Filips-Talums/Battery_Power_Monitor/docs/images/B1AA8C16-F89B-4345-A86B-DF6DE2874C3C.JPG

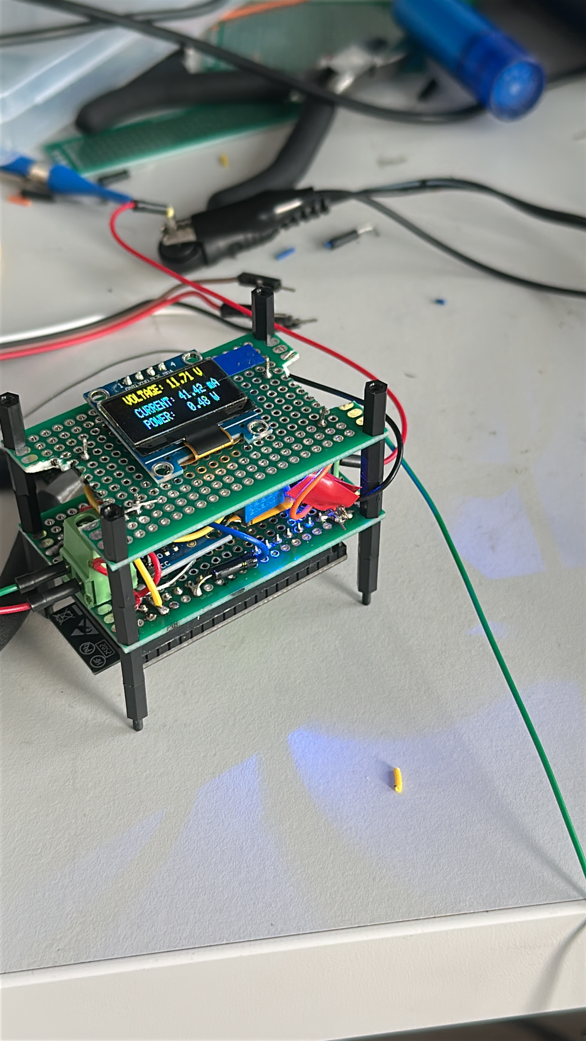
docs/images/B1AA8C16-F89B-4345-A86B-DF6DE2874C3C.JPG
