Filips-Talums/Battery_Power_Monitor/docs/images/IMG_2541.jpeg

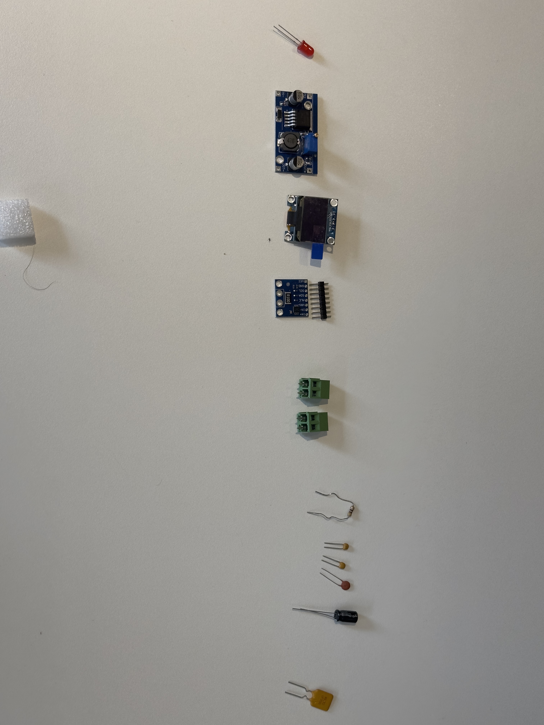
docs/images/IMG_2541.jpeg
