Filips-Talums/Battery_Power_Monitor/docs/images/IMG_2542.jpeg

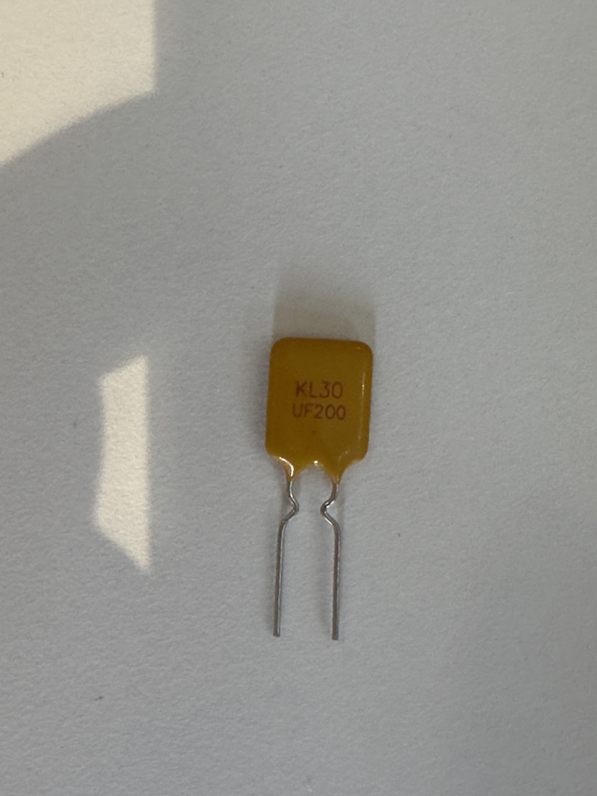
docs/images/IMG_2542.jpeg
