Filips-Talums/Battery_Power_Monitor/docs/images/IMG_2543.jpeg

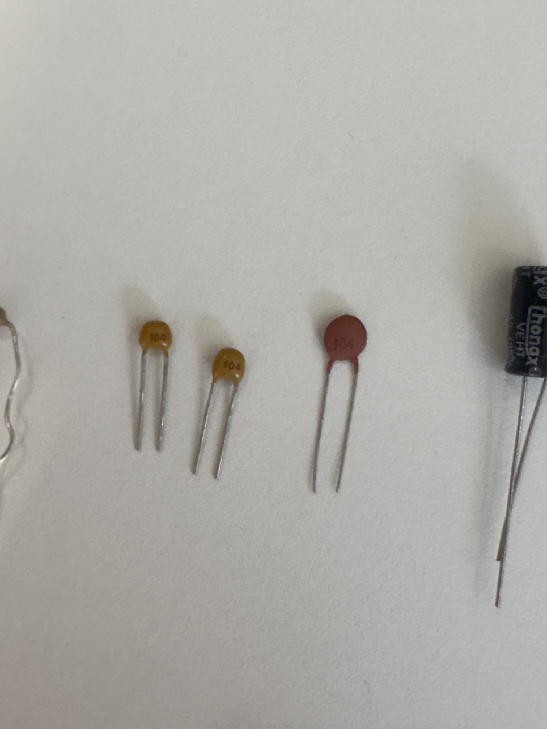
docs/images/IMG_2543.jpeg
