Filips-Talums/Battery_Power_Monitor/docs/images/IMG_2544.jpeg

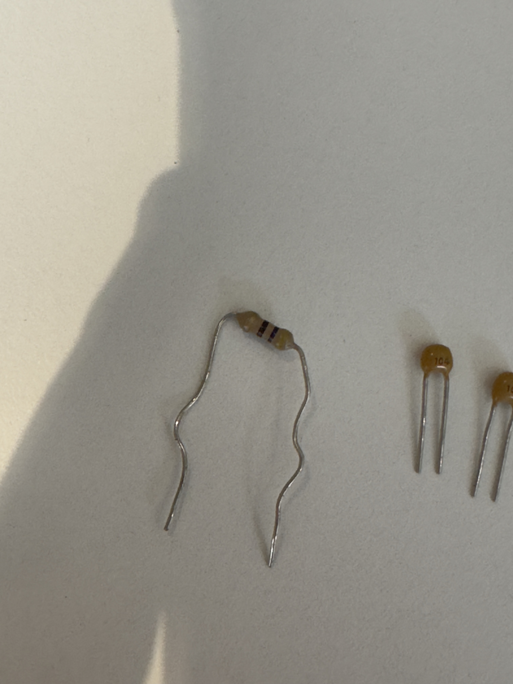
docs/images/IMG_2544.jpeg
