Filips-Talums/Battery_Power_Monitor/docs/images/IMG_2545.jpeg

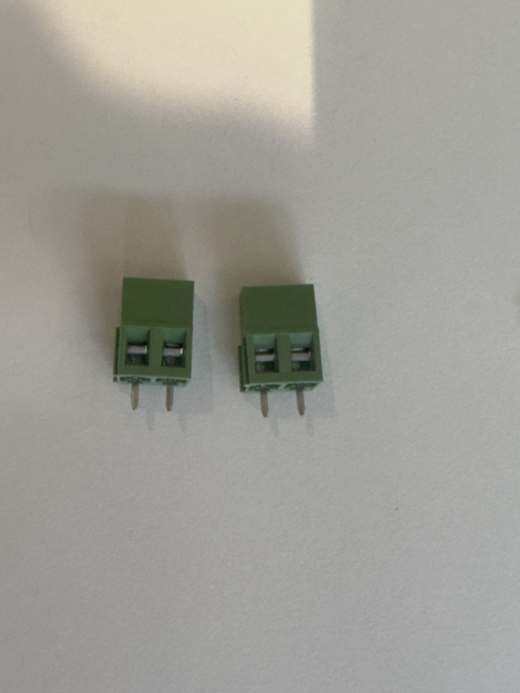
docs/images/IMG_2545.jpeg
