Filips-Talums/Battery_Power_Monitor/docs/images/IMG_2547.jpeg

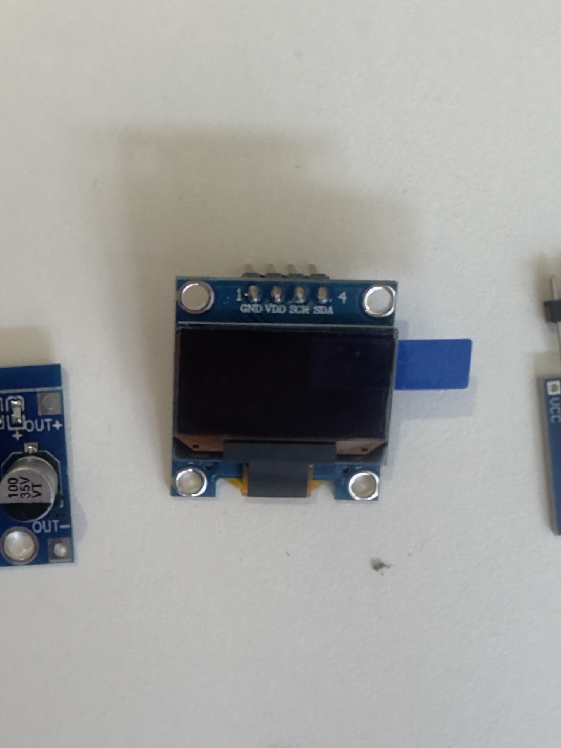
docs/images/IMG_2547.jpeg
