Filips-Talums/Battery_Power_Monitor/docs/images/IMG_2548.jpeg

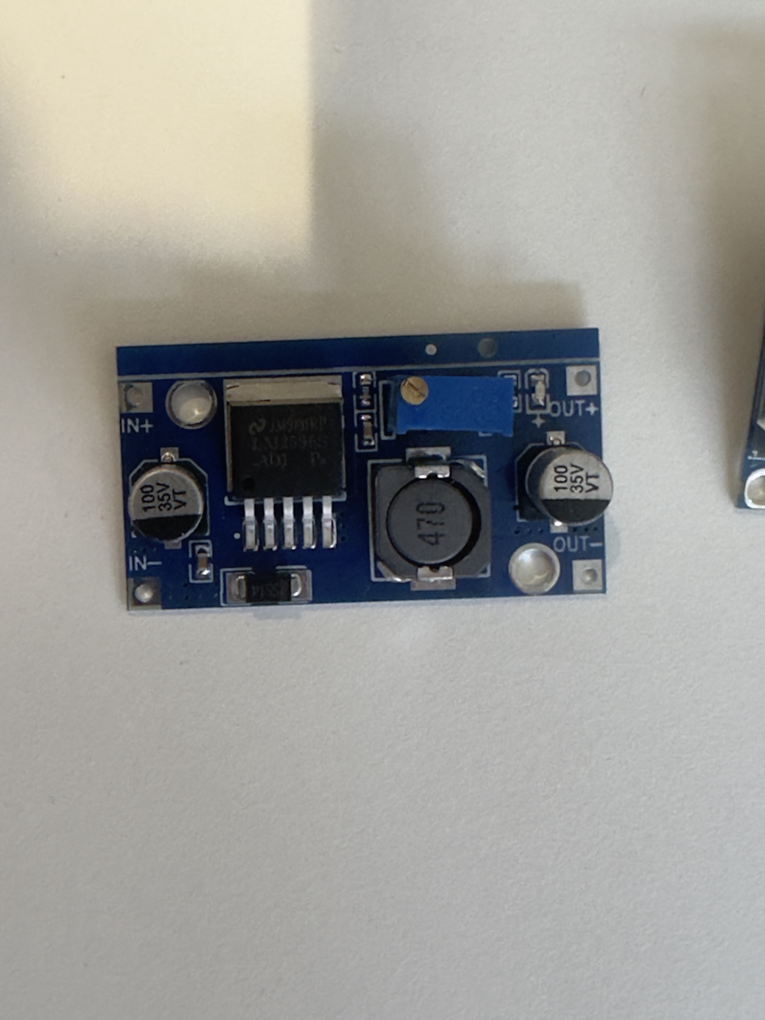
docs/images/IMG_2548.jpeg
