Filips-Talums/Battery_Power_Monitor/docs/images/IMG_2549.jpeg

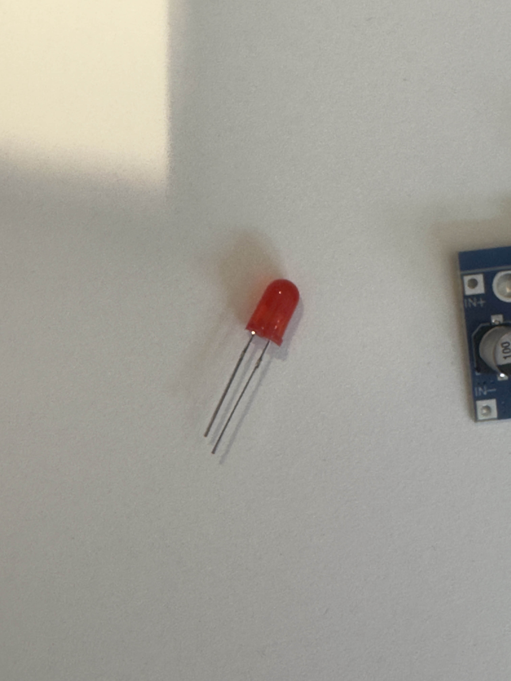
docs/images/IMG_2549.jpeg
