Filips-Talums/Battery_Power_Monitor/docs/images/IMG_2552.jpeg

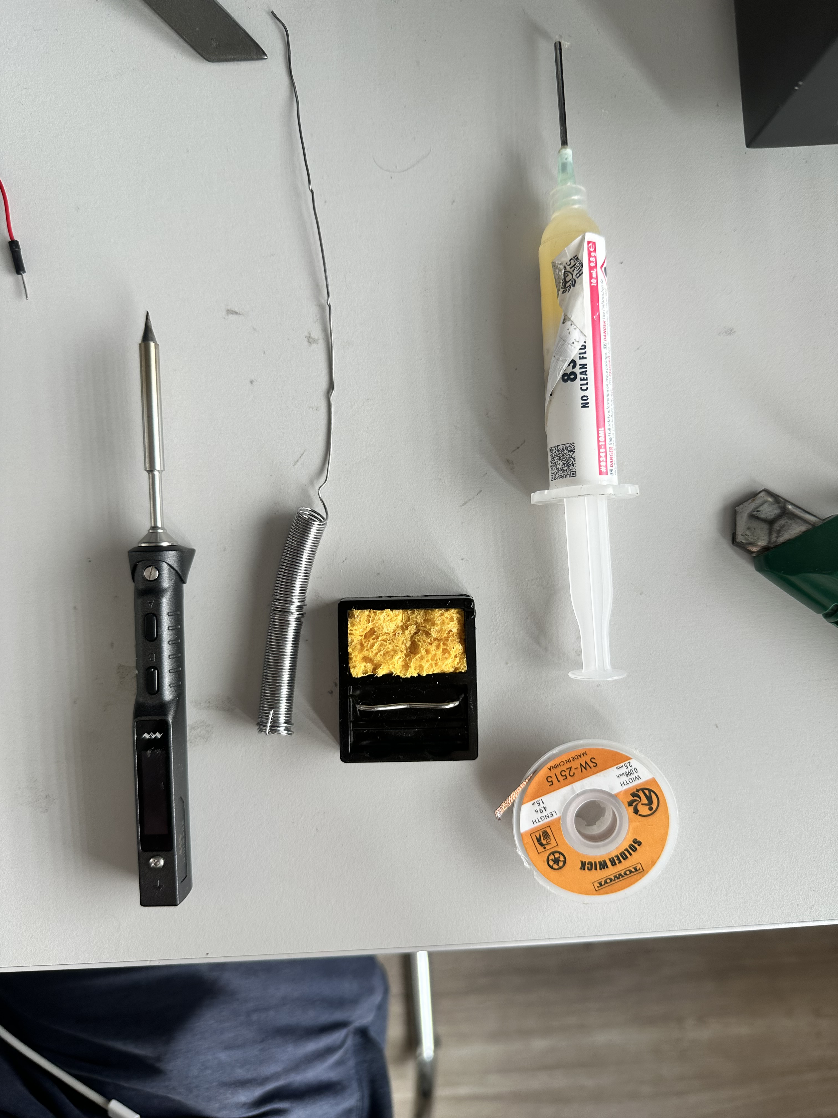
docs/images/IMG_2552.jpeg
