Filips-Talums/Battery_Power_Monitor/docs/images/IMG_2553.jpeg

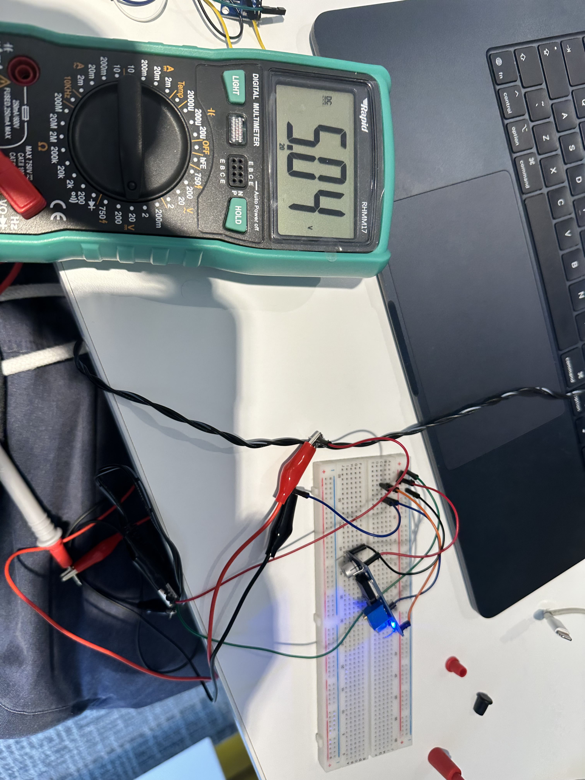
docs/images/IMG_2553.jpeg
