Filips-Talums/Battery_Power_Monitor/docs/images/IMG_2556.jpeg

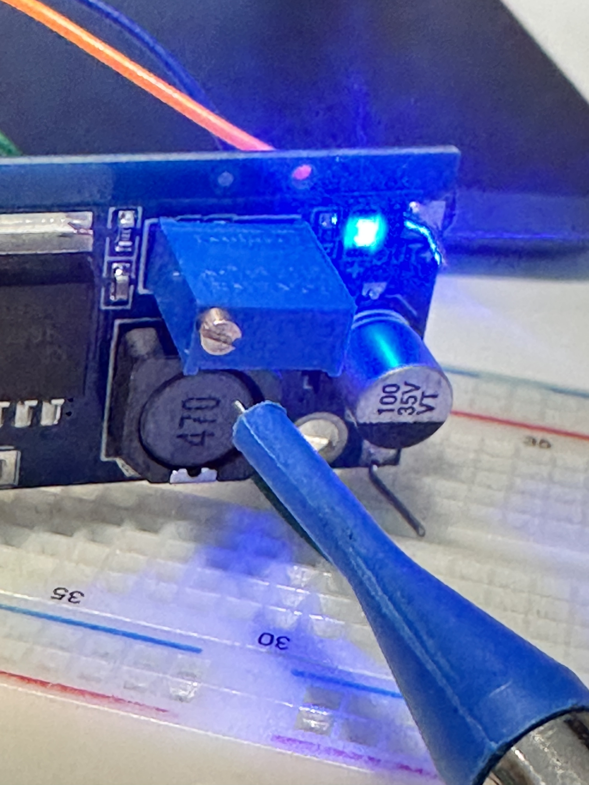
docs/images/IMG_2556.jpeg
