Filips-Talums/Battery_Power_Monitor/docs/images/IMG_2557.jpeg

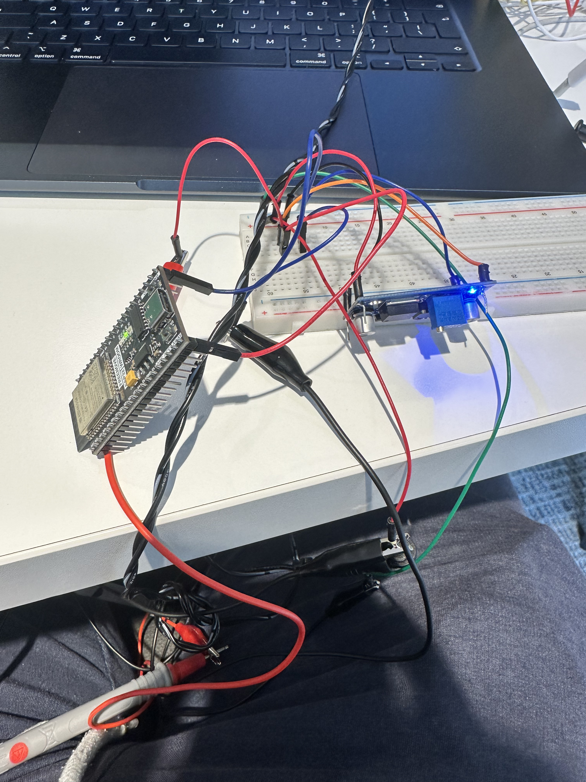
docs/images/IMG_2557.jpeg
