Filips-Talums/Battery_Power_Monitor/docs/images/IMG_2558.jpeg

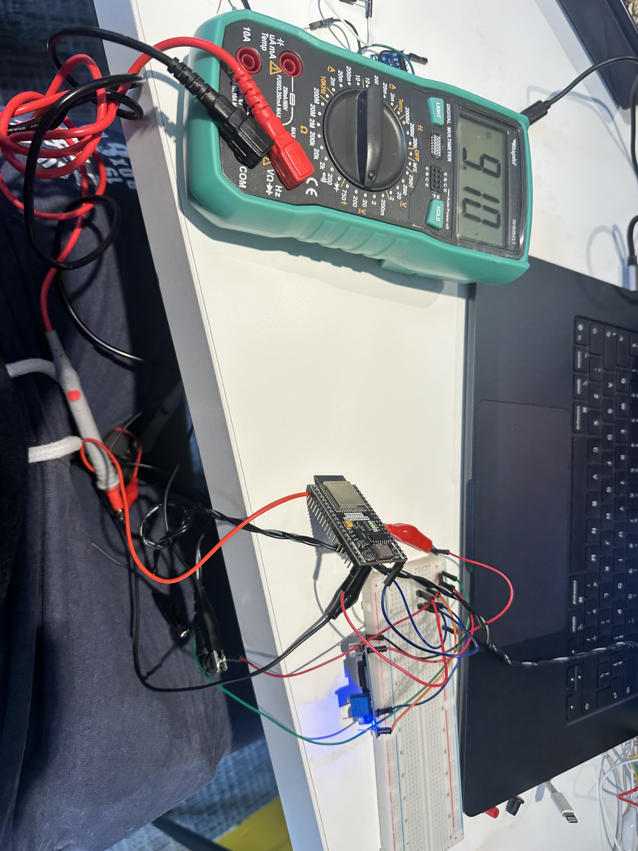
docs/images/IMG_2558.jpeg
