Filips-Talums/Battery_Power_Monitor/docs/images/IMG_2560.jpeg

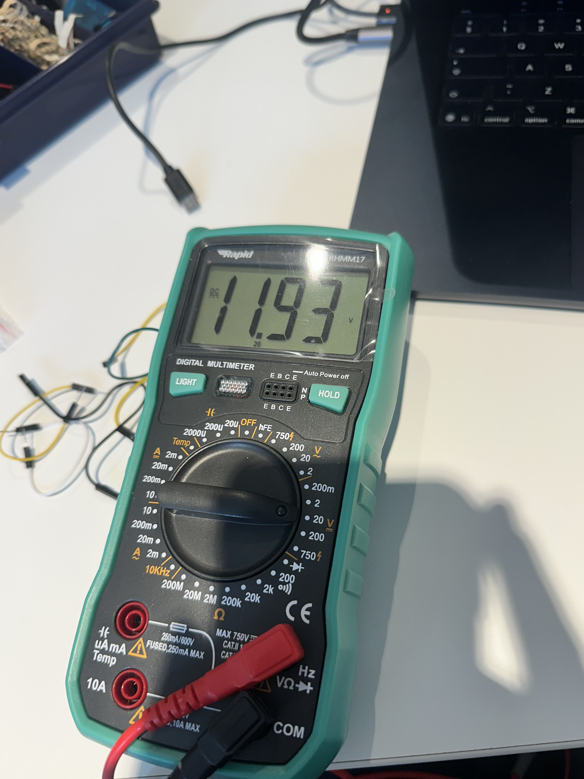
docs/images/IMG_2560.jpeg
