Filips-Talums/Battery_Power_Monitor/docs/images/IMG_2561.jpeg

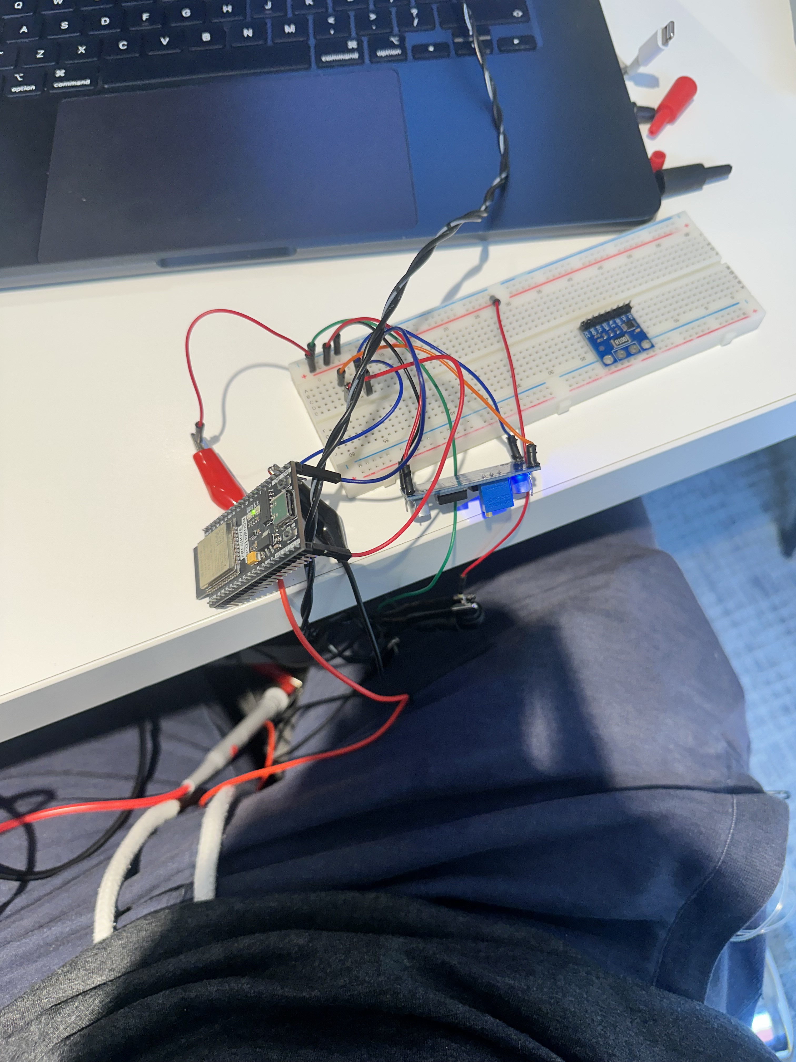
docs/images/IMG_2561.jpeg
