Filips-Talums/Battery_Power_Monitor/docs/images/IMG_2562.jpeg

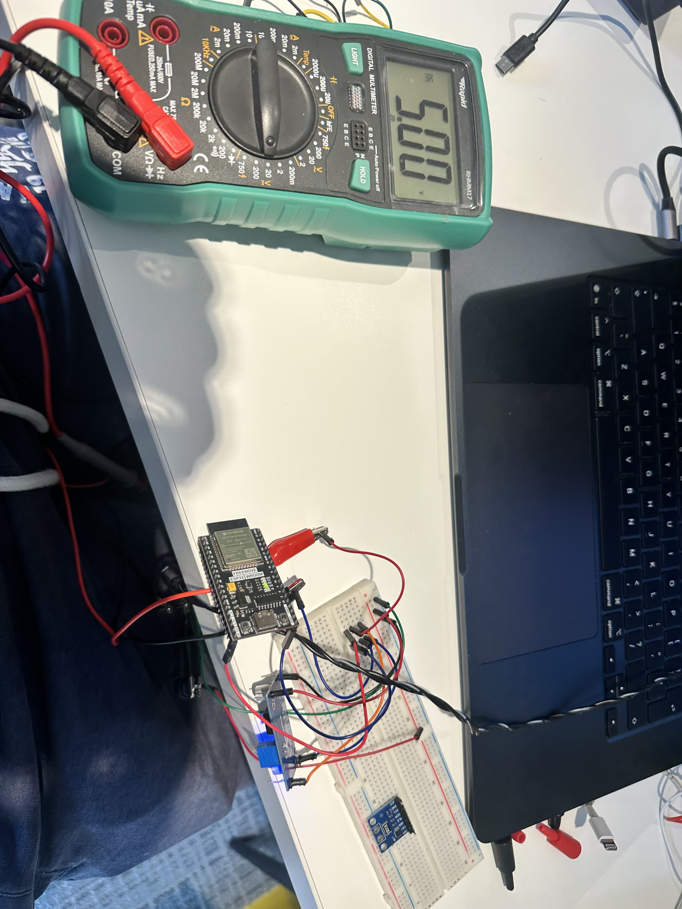
docs/images/IMG_2562.jpeg
