Filips-Talums/Battery_Power_Monitor/docs/images/IMG_2564.jpeg

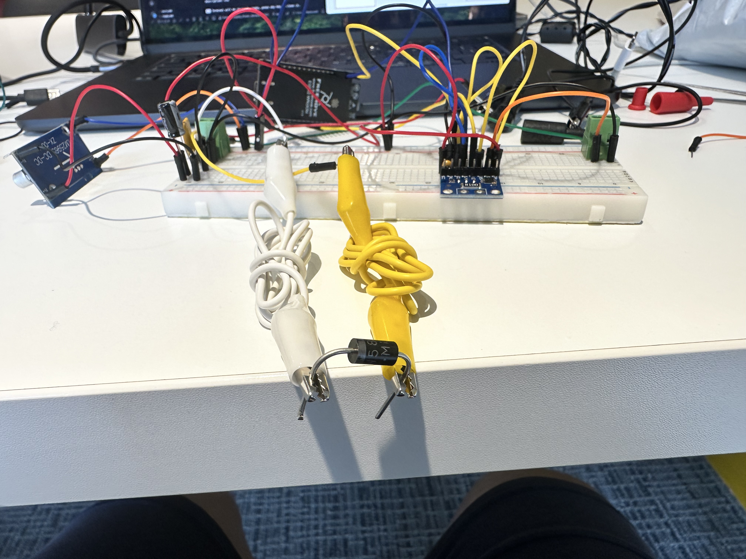
docs/images/IMG_2564.jpeg
