Filips-Talums/Battery_Power_Monitor/docs/images/IMG_2565.jpeg

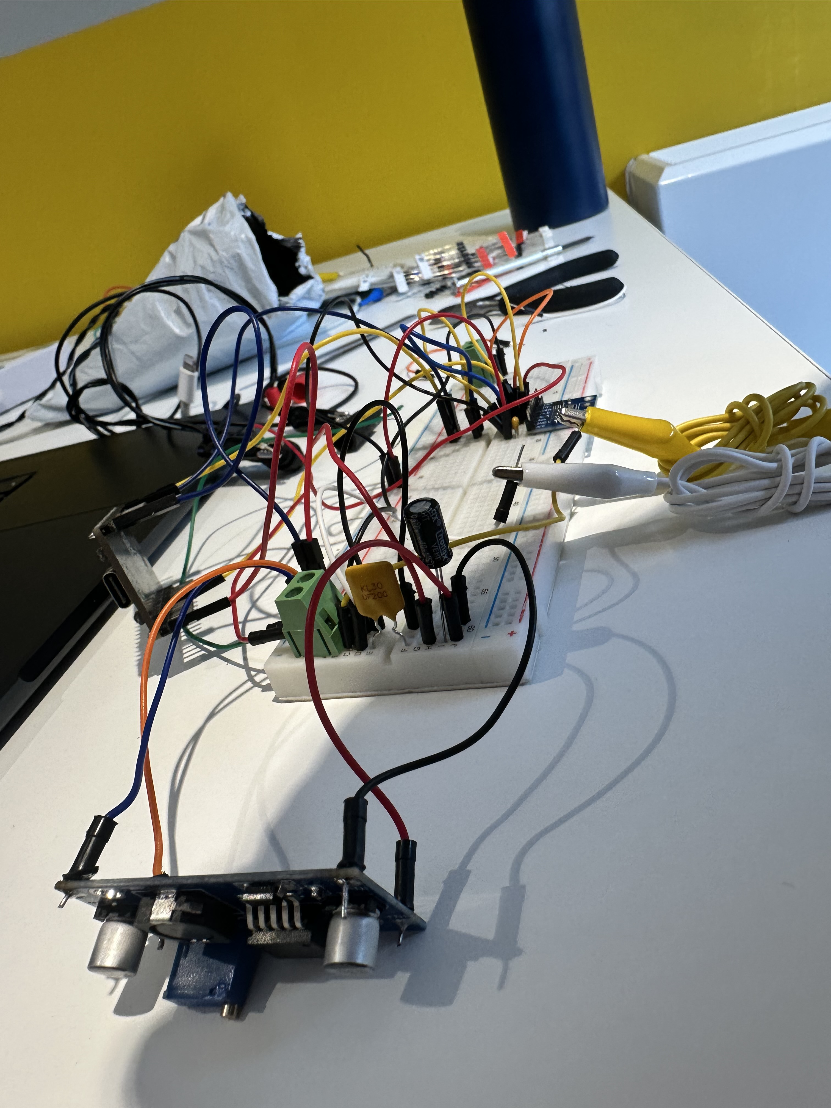
docs/images/IMG_2565.jpeg
