Filips-Talums/Battery_Power_Monitor/docs/images/IMG_2569.jpeg

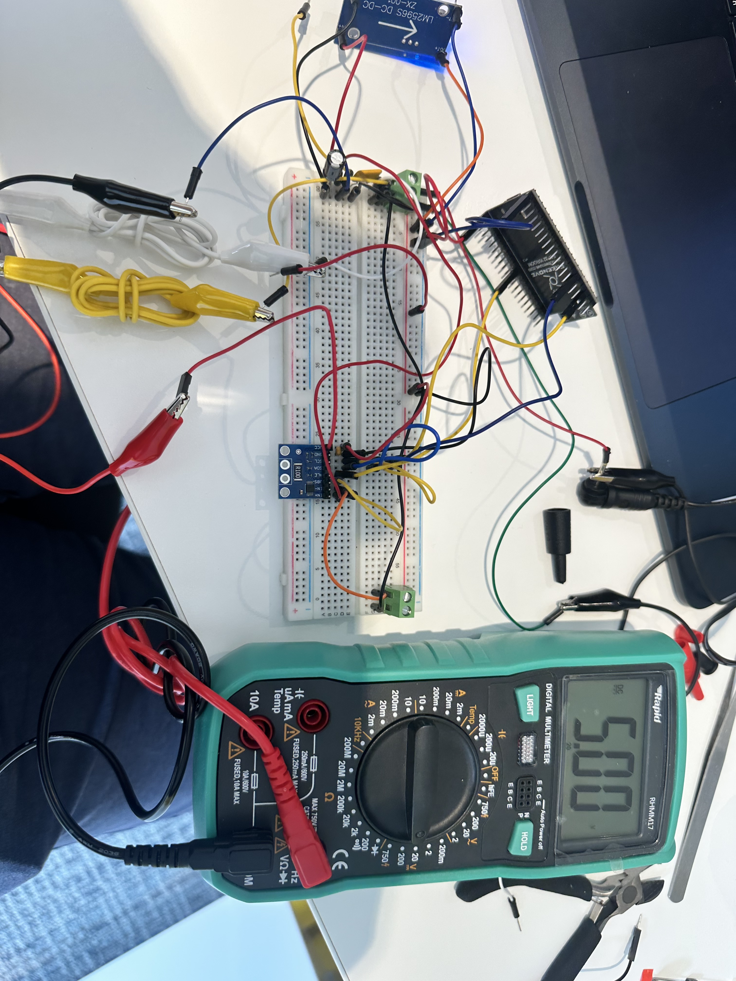
docs/images/IMG_2569.jpeg
