Filips-Talums/Battery_Power_Monitor/docs/images/IMG_2570.jpeg

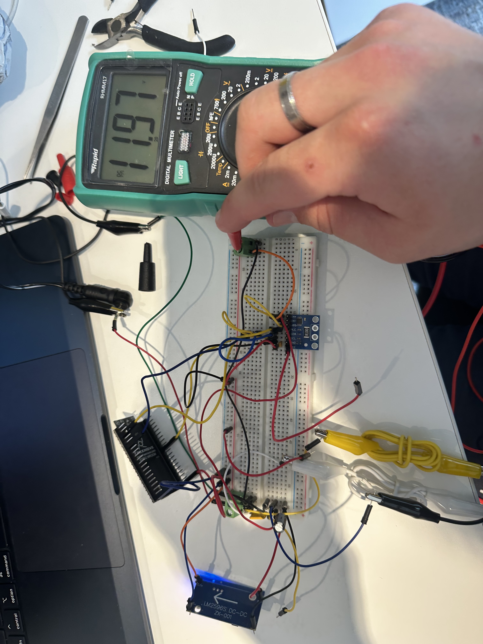
docs/images/IMG_2570.jpeg
