Filips-Talums/Battery_Power_Monitor/docs/images/IMG_2572.jpeg

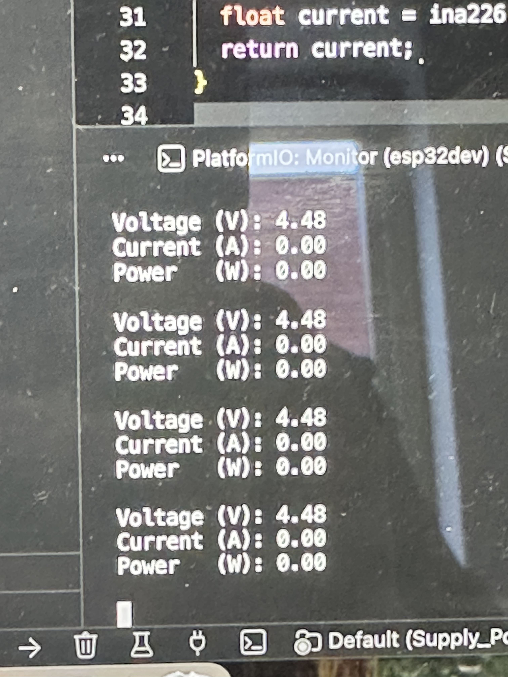
docs/images/IMG_2572.jpeg
