Filips-Talums/Battery_Power_Monitor/docs/images/IMG_2585.jpeg

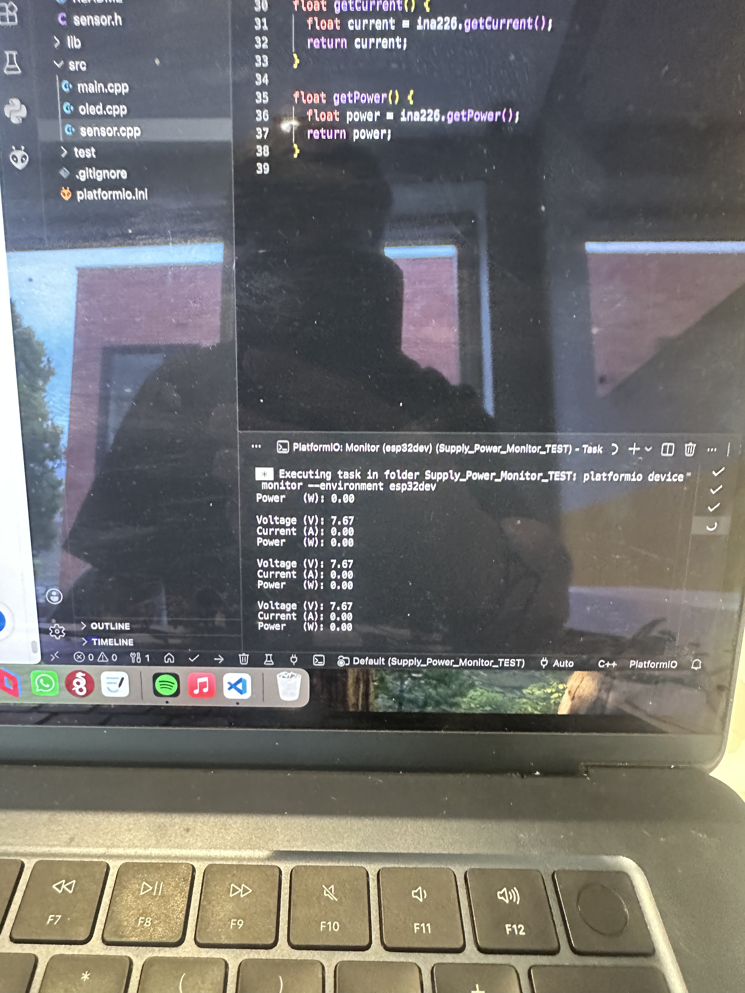
docs/images/IMG_2585.jpeg
