Filips-Talums/Battery_Power_Monitor/docs/images/IMG_2586.jpeg

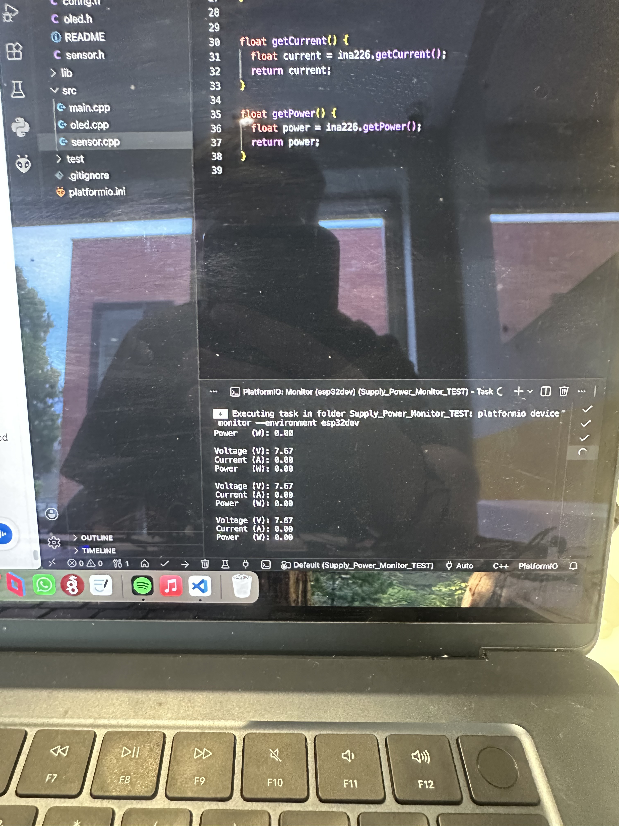
docs/images/IMG_2586.jpeg
