Filips-Talums/Battery_Power_Monitor/docs/images/IMG_2587.jpeg

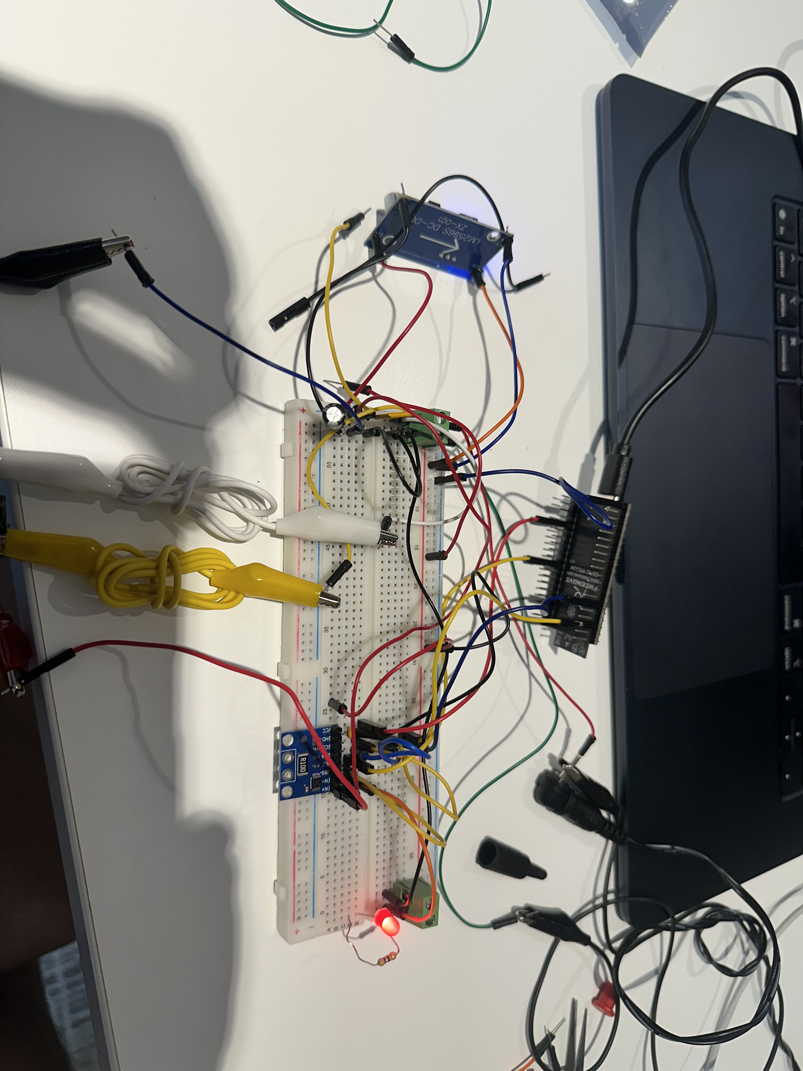
docs/images/IMG_2587.jpeg
