Filips-Talums/Battery_Power_Monitor/docs/images/IMG_2588.jpeg

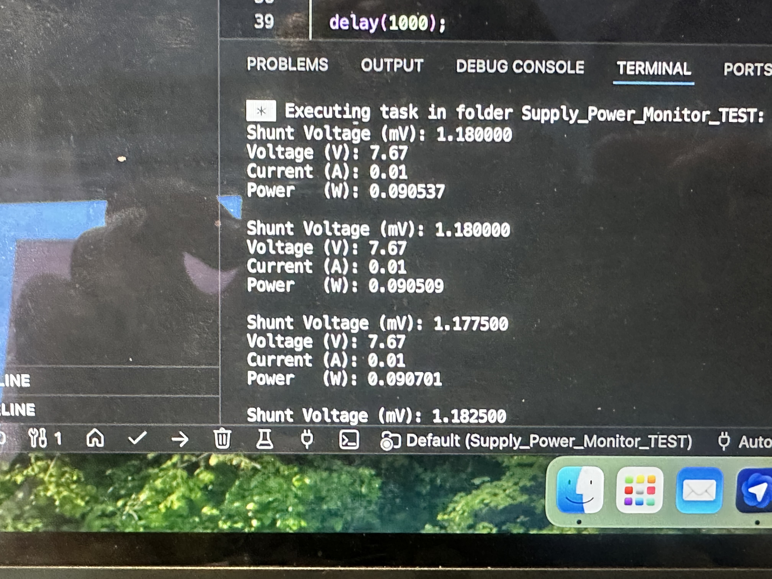
docs/images/IMG_2588.jpeg
