Filips-Talums/Battery_Power_Monitor/docs/images/IMG_2617.jpeg

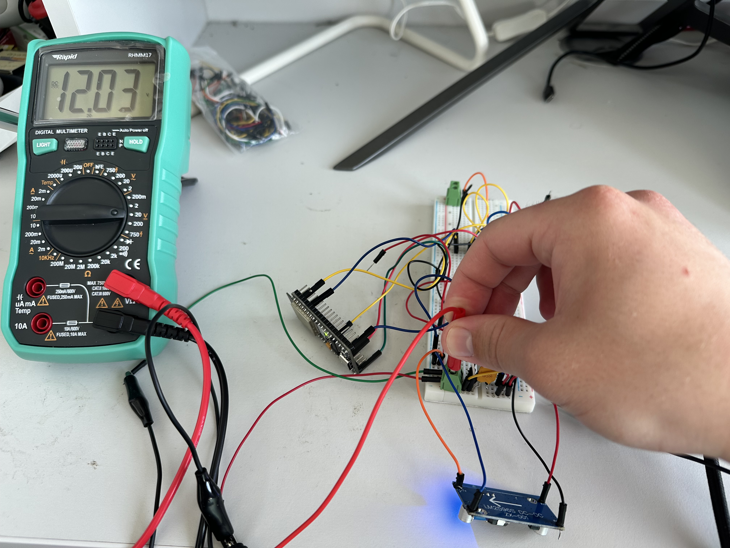
docs/images/IMG_2617.jpeg
