Filips-Talums/Battery_Power_Monitor/docs/images/IMG_2618.jpeg

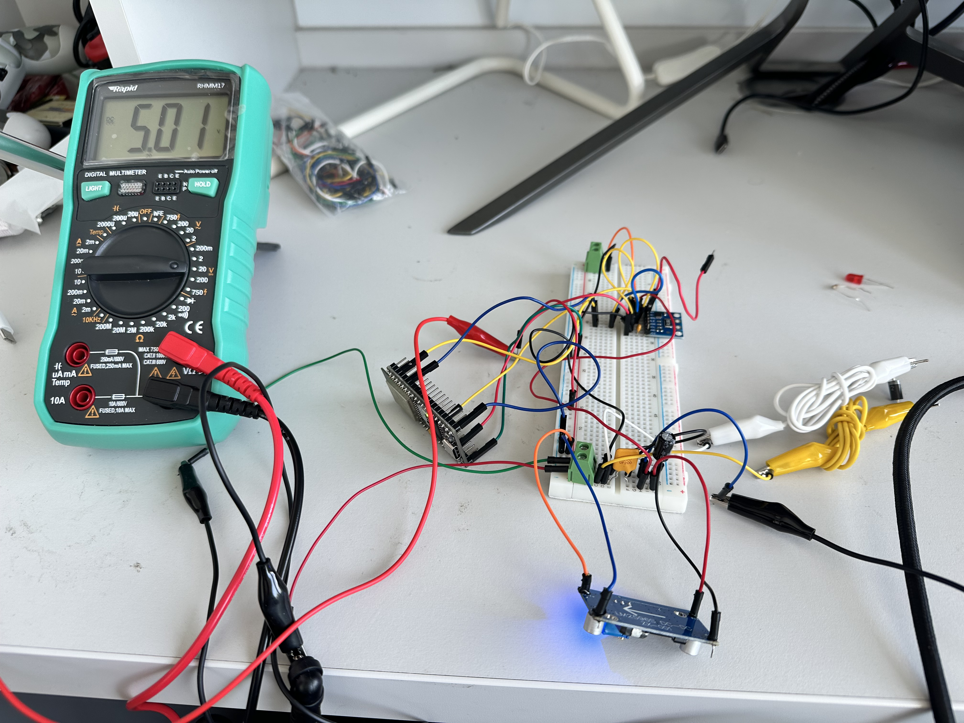
docs/images/IMG_2618.jpeg
