Filips-Talums/Battery_Power_Monitor/docs/images/IMG_2619.jpeg

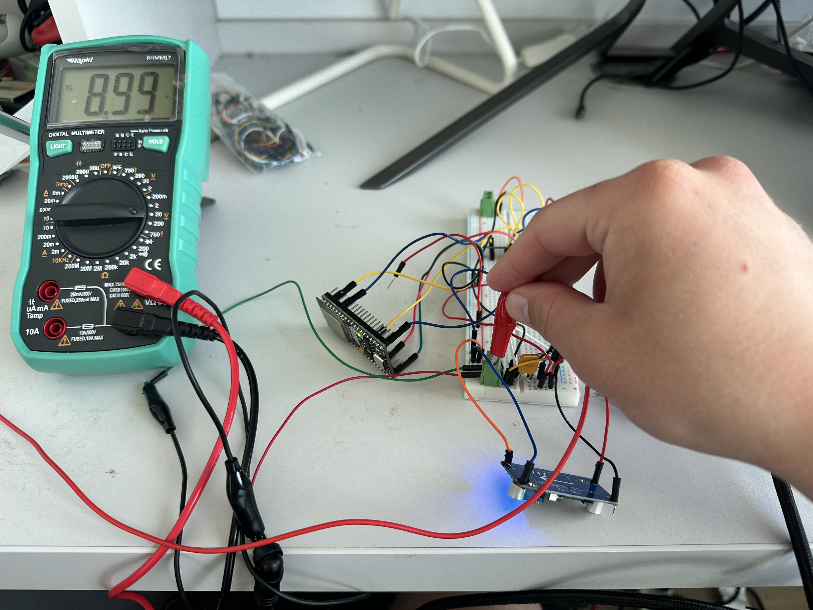
docs/images/IMG_2619.jpeg
