Filips-Talums/Battery_Power_Monitor/docs/images/IMG_2622.jpeg

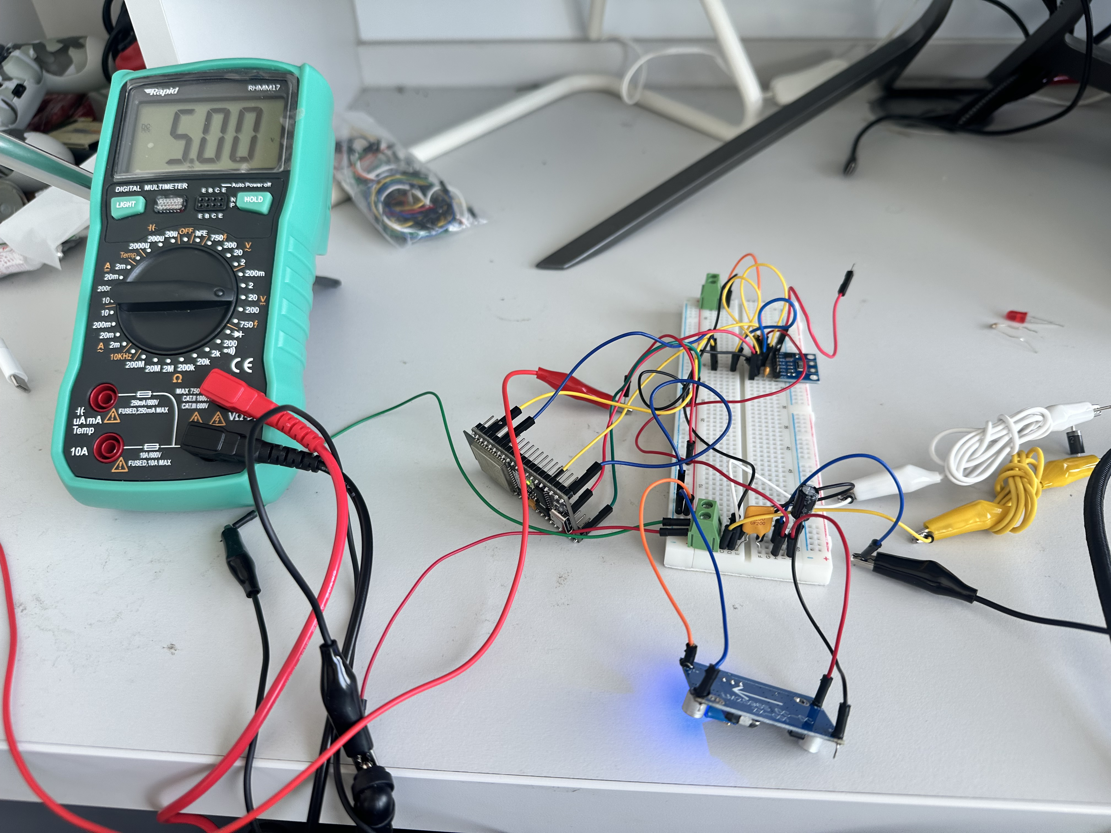
docs/images/IMG_2622.jpeg
