Filips-Talums/Battery_Power_Monitor/docs/images/IMG_2623.jpeg

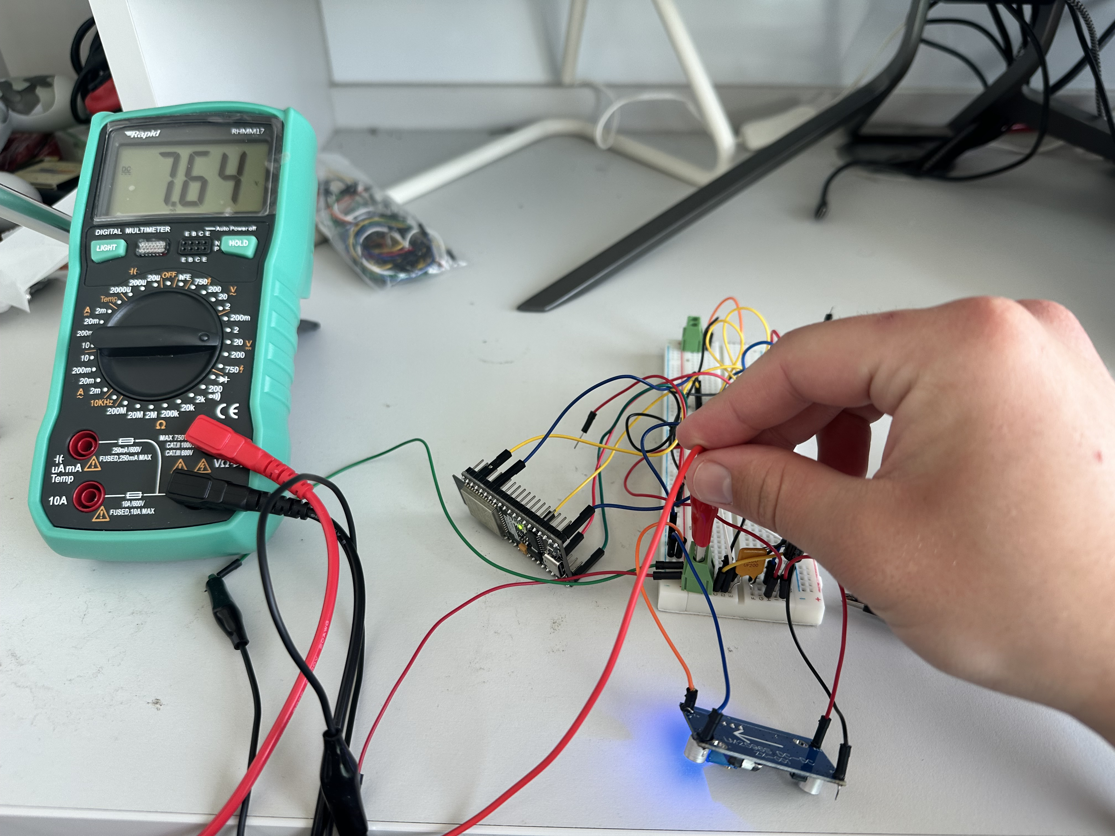
docs/images/IMG_2623.jpeg
