Filips-Talums/Battery_Power_Monitor/docs/images/IMG_2625.jpeg

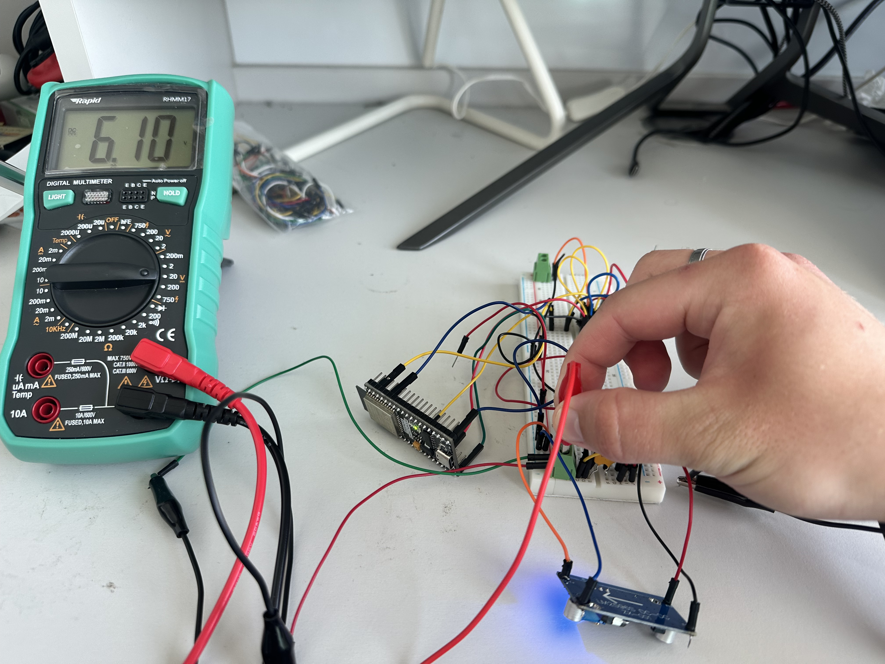
docs/images/IMG_2625.jpeg
