Filips-Talums/Battery_Power_Monitor/docs/images/IMG_2626.jpeg

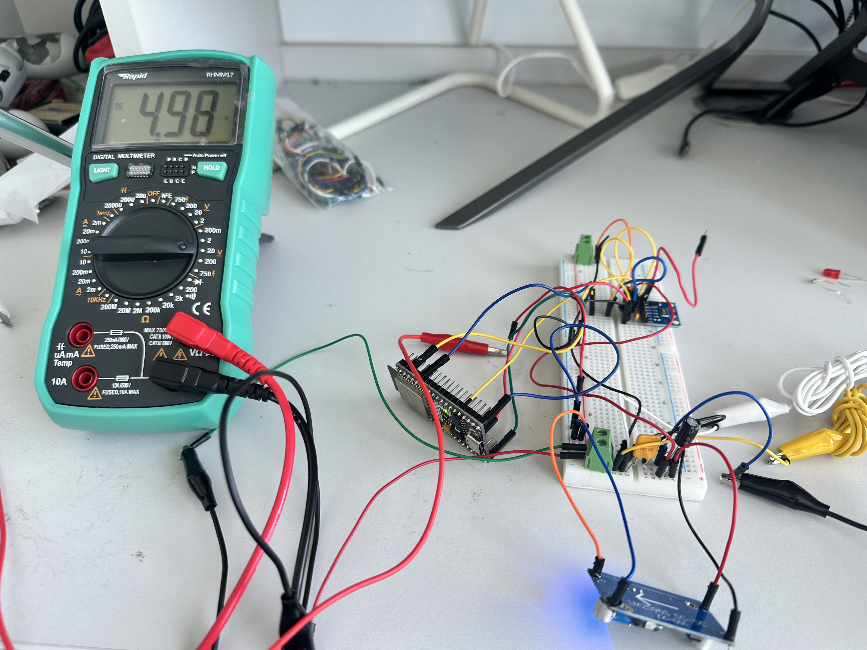
docs/images/IMG_2626.jpeg
