Filips-Talums/Battery_Power_Monitor/docs/images/IMG_2627.jpeg

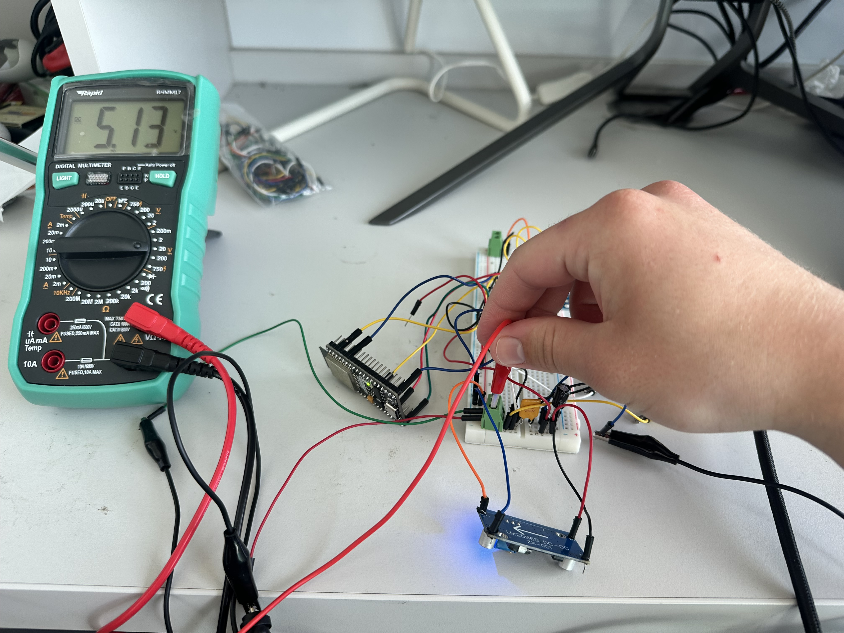
docs/images/IMG_2627.jpeg
