Filips-Talums/Battery_Power_Monitor/docs/images/IMG_2629.jpeg

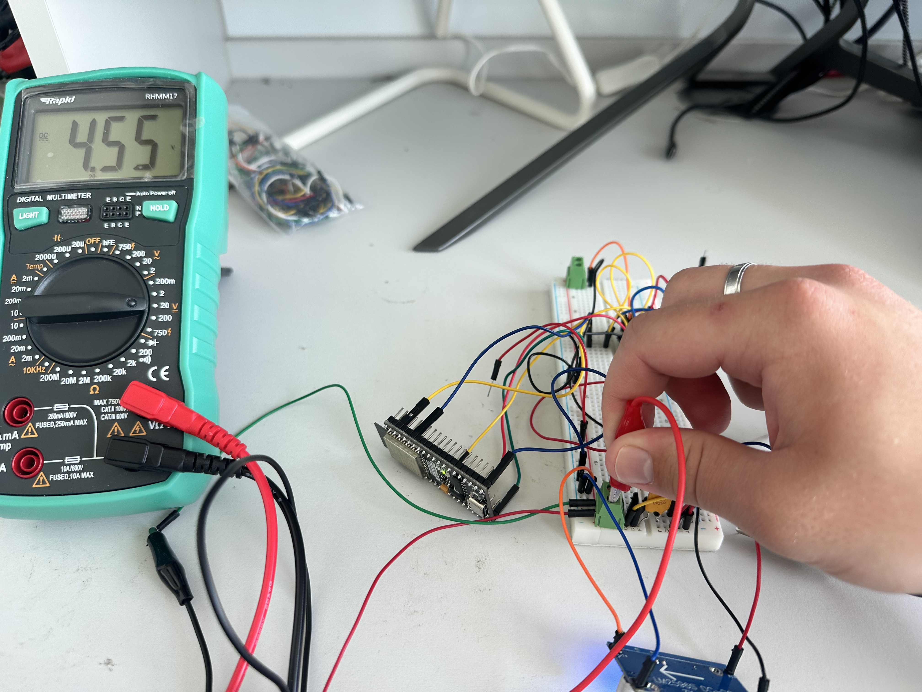
docs/images/IMG_2629.jpeg
