Filips-Talums/Battery_Power_Monitor/docs/images/IMG_2630.jpeg

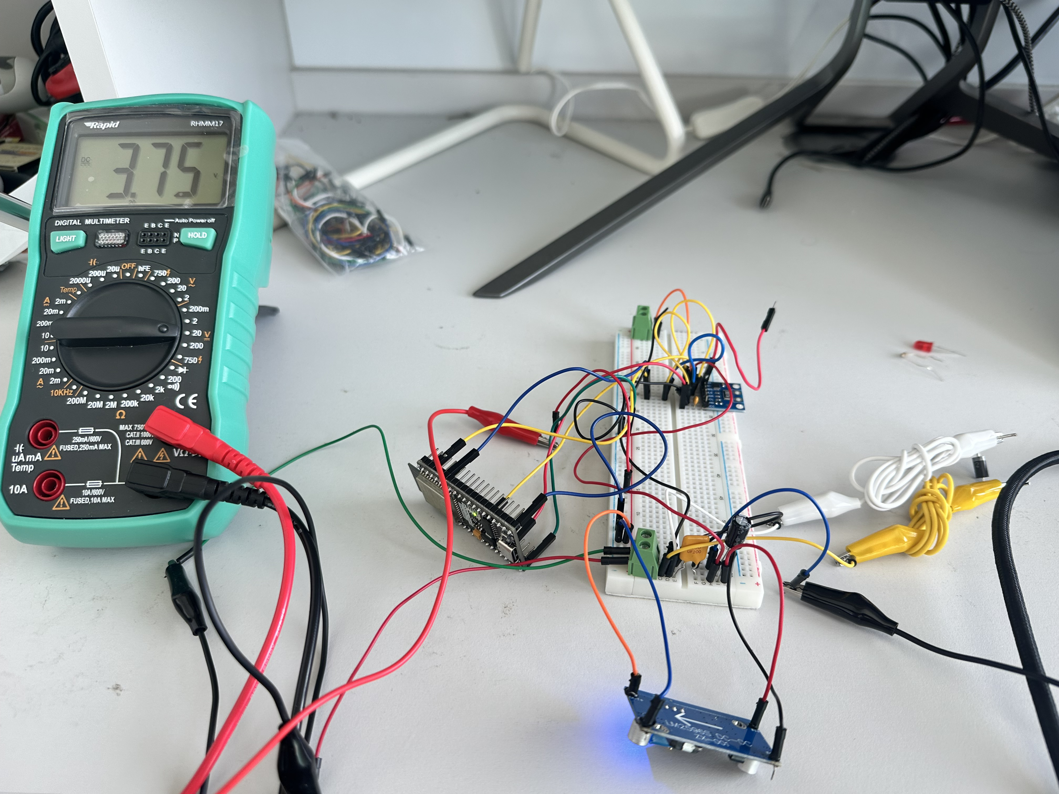
docs/images/IMG_2630.jpeg
