Filips-Talums/Battery_Power_Monitor/docs/images/IMG_2633.jpeg

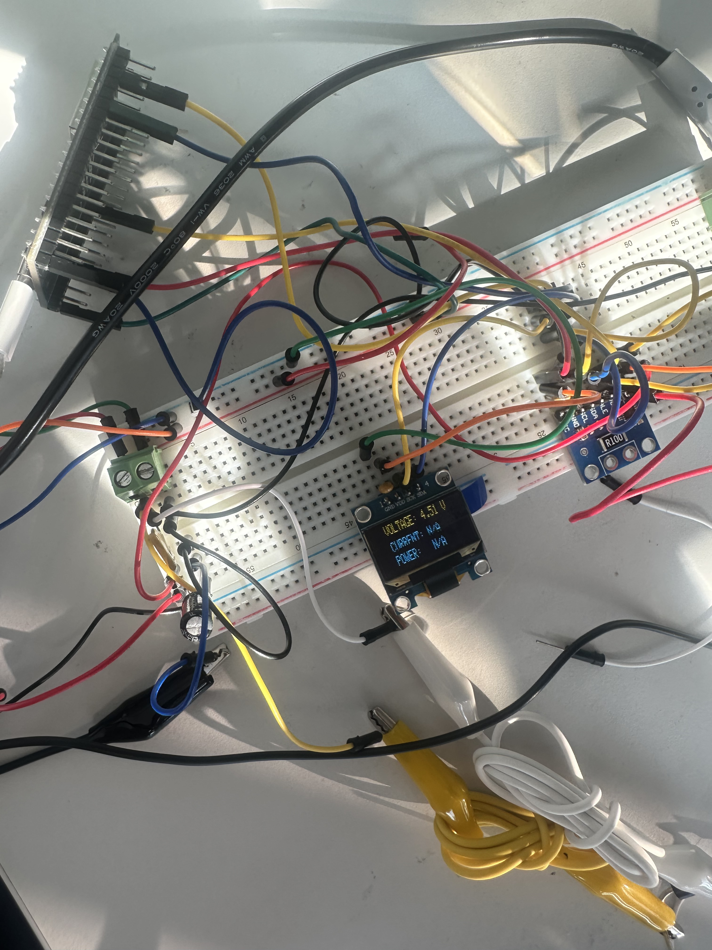
docs/images/IMG_2633.jpeg
