Filips-Talums/Battery_Power_Monitor/docs/images/IMG_2771.jpeg

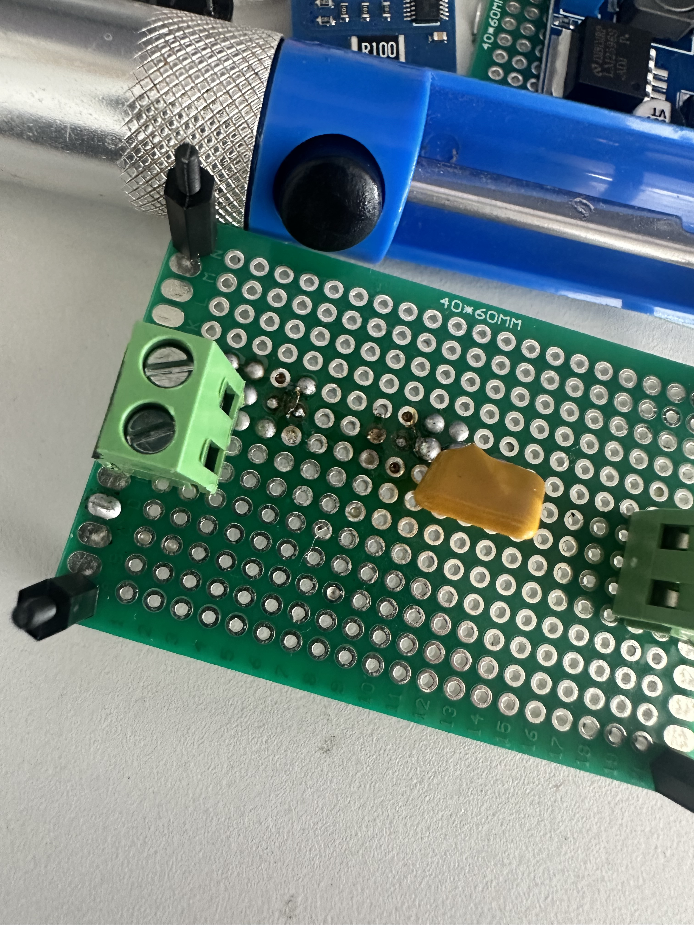
docs/images/IMG_2771.jpeg
