Filips-Talums/Battery_Power_Monitor/docs/images/IMG_2772.jpeg

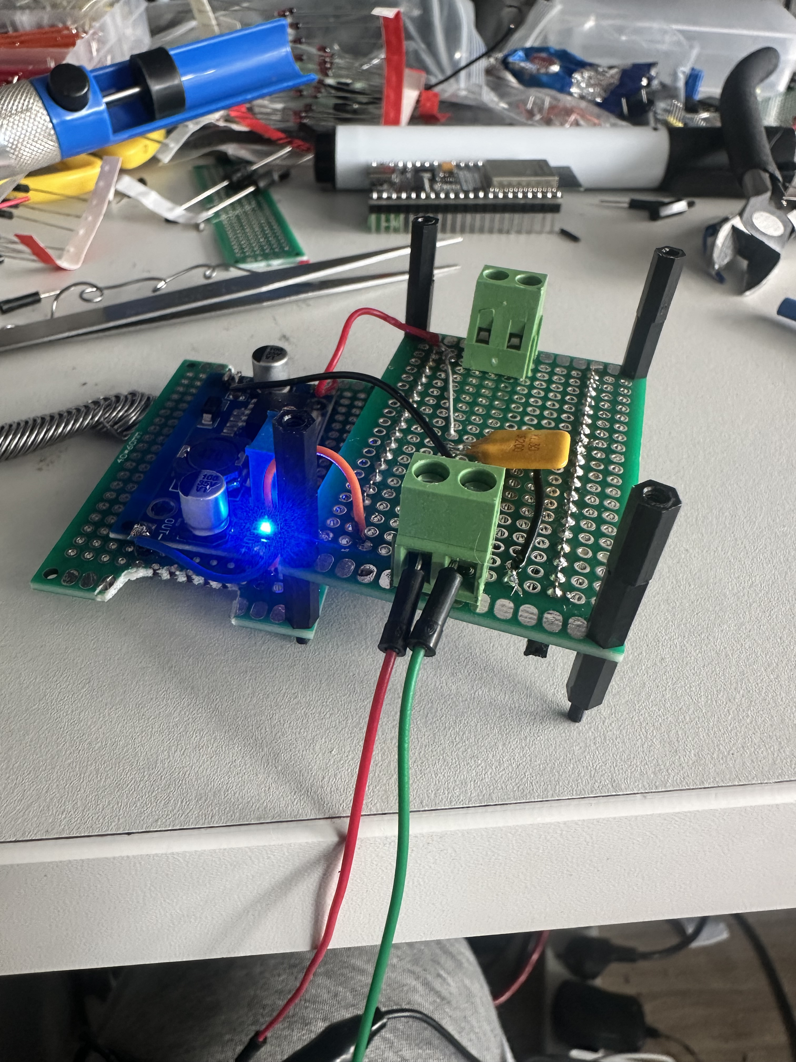
docs/images/IMG_2772.jpeg
