Filips-Talums/Battery_Power_Monitor/docs/images/IMG_2773.jpeg

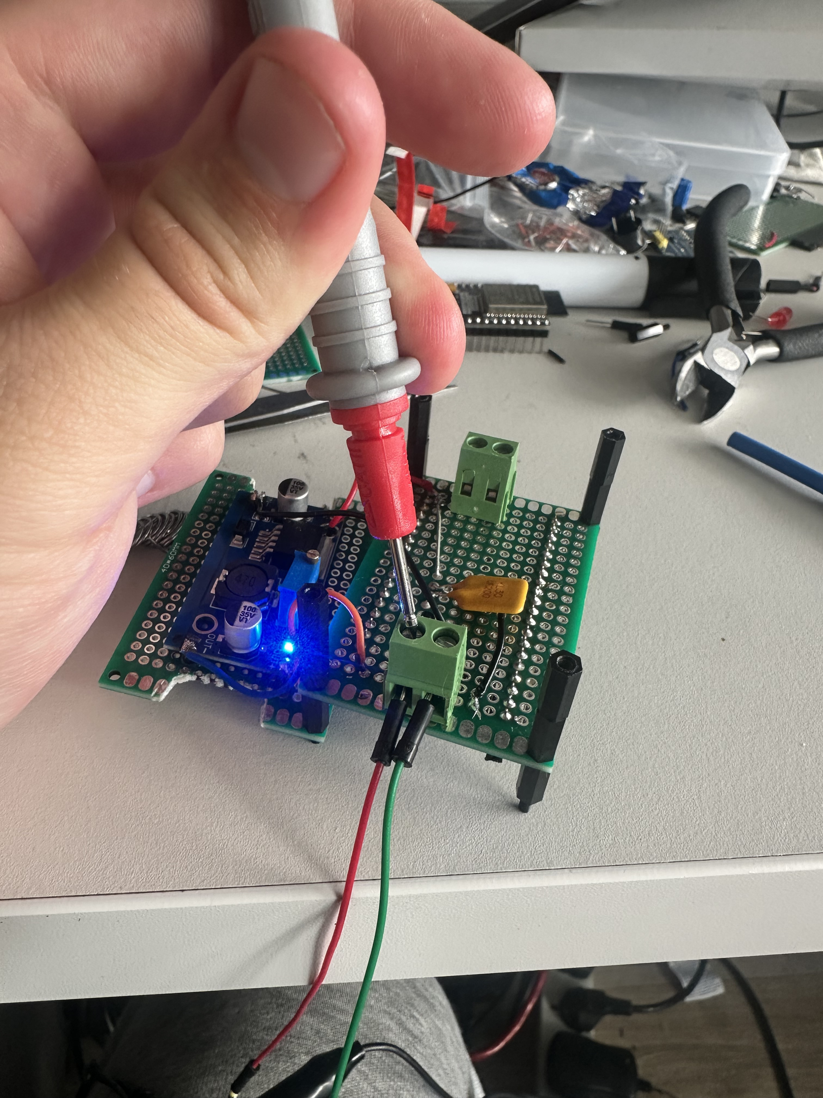
docs/images/IMG_2773.jpeg
