Filips-Talums/Battery_Power_Monitor/docs/images/IMG_2774.jpeg

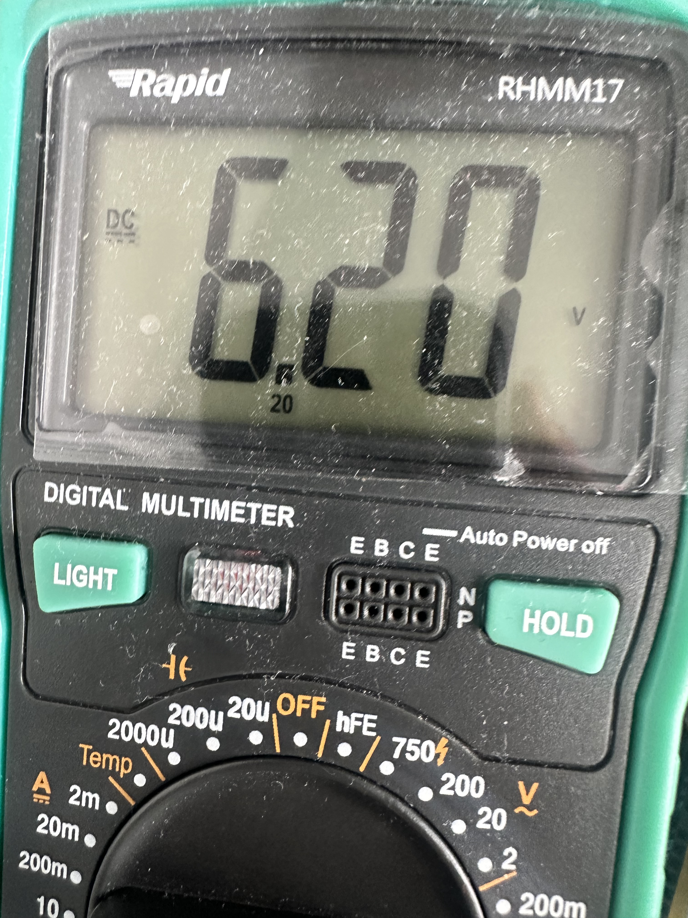
docs/images/IMG_2774.jpeg
