Filips-Talums/Battery_Power_Monitor/docs/images/IMG_2799.jpeg

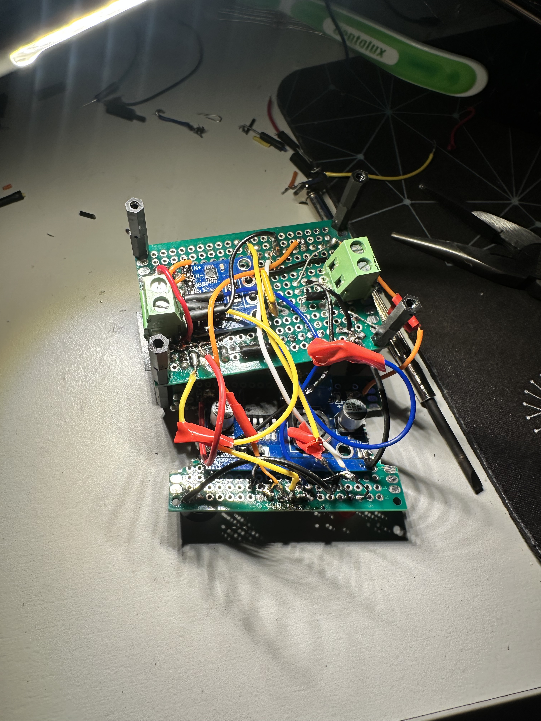
docs/images/IMG_2799.jpeg
