Filips-Talums/Battery_Power_Monitor/docs/images/IMG_2584.jpeg

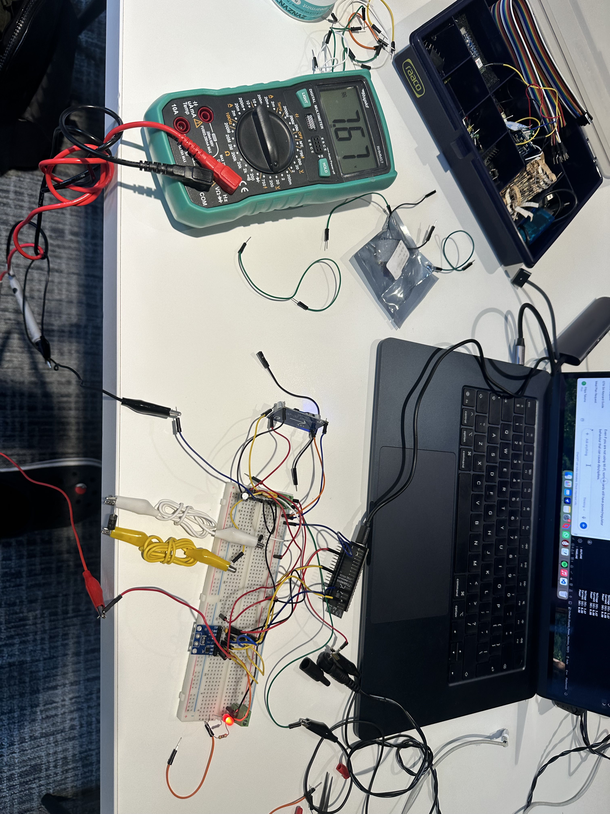
docs/images/IMG_2584.jpeg
